jeffdhooton/jingis38/graphics/pcb-graphic-2.png

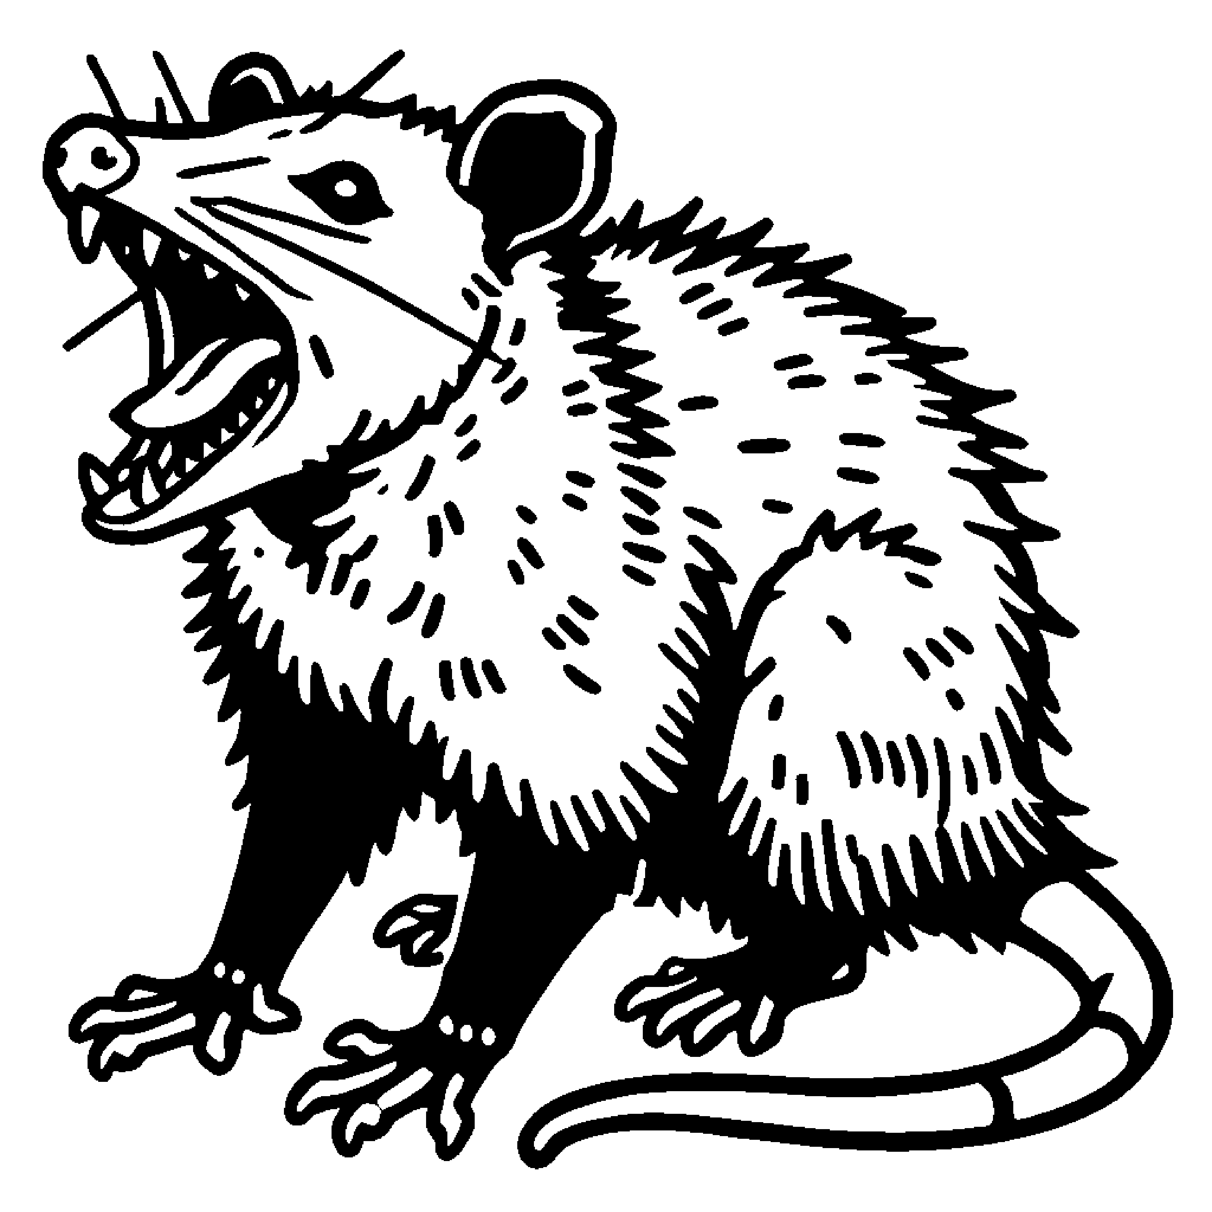
graphics/pcb-graphic-2.png
